BradenMeyers/Unzipper/NON CODE/CAD files/STL/48T Pulley v1.stl

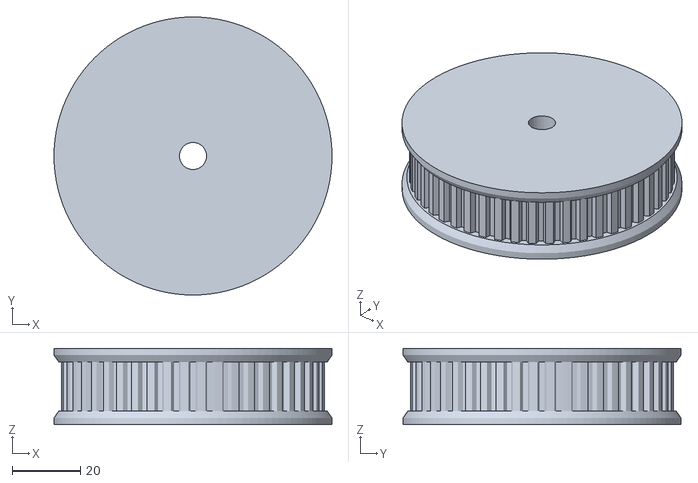
[picture p19: CAD file, 2022-12-04]
NON CODE/CAD files/STL/48T Pulley v1.stl
81.4 x 81.4 x 22.3
