BradenMeyers/Unzipper/src/serverESP.cpp

#include <Arduino.h>
#include <WiFi.h>
#include <AsyncTCP.h>
#include <ESPAsyncWebServer.h>
#include <serverESP.h>
#include <SPIFFS.h>
#include <accelerometer.h>
#include <testCases.h>
#include <odometer.h>
#include <gps.h>
#include <servoBrake.h>

Blogger logger;

typedef enum{
    ACCELEROMETER,
    ODOMETER, 
    LED,
    MOTOR,
    SERVO
} server_test;
server_test testServer = LED;

//#include <constants.h>
#include <Preferences.h>
Preferences preferences;
#include <timer.h>
Timer batterycheck;

const char* ssid = "Zip-Line-Controls";
const char* password = "123456789";

byte batteryMonitor = 34;
byte odometerSensor = 33;

byte state = READY;
int odometerSensorValue = 0;
int motorsMaxSpeed = 200;
float afterZipDelay = 7;

int highThreshold = 3000;
String highThresholdStr = String(highThreshold);
int lowThreshold = 300;
String lowThresholdStr = String(lowThreshold);

String stateStr = "Ready";
String directionStr = "UP";
String motorMaxSpeedStr = String(motorsMaxSpeed);
String afterZipDelayStr = String(afterZipDelay);  //cause actual variable is in miliseconds but wifi is in seconds
String uprightErrorStr = String(uprightError);
String gpsErrorStr = String(gpsError);
String stopPosServoStr = String(stopPosServo);

bool wifiStopMotor = false;
bool wifiSkipToRecovery = false;

AsyncWebServer server(80);

float batteryVoltage(){
    float reading = analogRead(batteryMonitor);
    reading = ((reading)/(4095)) * 25.6;  //calibrated on May 24 2023
    static float voltage = 19.68;
    float alpha = 0.8;
    voltage = voltage*alpha + (1-alpha)*reading;
    return voltage;
}

// Replaces placeholder with button section in your web page
String processor(const String& var){
  //logln(var);
  if (var == "MAXSPEEDVALUE"){return String(motorsMaxSpeed);}
  else if(var == "STATE"){return stateStr;}
  else if(var == "DIRECTION"){return directionStr;}
  else if(var == "AFTERZIPDELAY"){return afterZipDelayStr;}
  else if(var == "LOWTHRESHOLD"){return lowThresholdStr;}
  else if(var == "HIGHTHRESHOLD"){return highThresholdStr;}
  else if(var == "UPRIGHTERROR"){return String(uprightError);}
  else if(var == "VOLTAGE") return String(batteryVoltage());
  else if(var == "TEMPERATURE") return String(getTemperature());
  else if(var == "LOGSTRING"){return logger.logStr.c_str();}
  else if(var == "TESTLOG"){return testLogger.logStr.c_str();}
  else if(var == "SATLOCK"){return String(satelliteLock());}
  else if(var == "GPSERROR"){return String(gpsError);}
  else if(var == "SERVOANGLE"){return String(stopPosServo);}
  return String();
}

void storeValues(){
    preferences.putUInt("lower", lowThreshold);
    preferences.putUInt("upper", highThreshold);
    preferences.putUInt("max", motorsMaxSpeed);
    preferences.putFloat("zDelay", afterZipDelay);
    preferences.putFloat("uError", uprightError);
    preferences.putFloat("gpsError", gpsError);
    preferences.putUInt("servoAngle", stopPosServo);
}

void initSPIFFS() {
  if (!SPIFFS.begin()) {
    Serial.println("An error has occurred while mounting SPIFFS");
  }
  Serial.println("SPIFFS mounted successfully");
}

void serverSetup(){
    preferences.begin("my-app", false);
    motorsMaxSpeed = preferences.getUInt("max", 195);     //max speed
    highThreshold = preferences.getUInt("upper", 2500); //Upper IR Threshold
    lowThreshold = preferences.getUInt("lower", 1000); //Lower IR threshold
    afterZipDelay = preferences.getFloat("zDelay", 10);  //Delay after the zipping state
    uprightError = preferences.getFloat("uError", 1.5);  //Delay after the zipping state
    gpsError = preferences.getFloat("gpsError", 3);  //Delay after the zipping state
    stopPosServo = preferences.getUInt("servoAngle", 133);  //Delay after the zipping state
    motorMaxSpeedStr = String(motorsMaxSpeed);
    afterZipDelayStr = String(afterZipDelay);
    lowThresholdStr = String(lowThreshold);
    highThresholdStr = String(highThreshold);
    uprightErrorStr = String(uprightError);
    gpsErrorStr = String(gpsError);
    stopPosServoStr = String(stopPosServo);
    WiFi.mode(WIFI_AP_STA);
    WiFi.softAP(ssid, password);
    server.begin();
    initSPIFFS();
    delay(3000);

    server.on("/", HTTP_GET, [](AsyncWebServerRequest *request){
        request->send(SPIFFS, "/index.html", String(), false, processor);
    });

    server.on("/maxspeed", HTTP_GET, [] (AsyncWebServerRequest *request){
        // GET input1 value on <ESP_IP>/slider?value=<inputMessage>
        if (request->hasParam("value")) {
        motorMaxSpeedStr = request->getParam("value")->value();
        motorsMaxSpeed = motorMaxSpeedStr.toInt();
        logger.log("Max speed in now: ", true);
        logger.log(motorMaxSpeedStr);
        }
        request->send(200, "text/plain", "OK");
    });

    server.on("/afterzipdelay", HTTP_GET, [] (AsyncWebServerRequest *request){
        // GET input1 value on <ESP_IP>/slider?value=<inputMessage>
        if (request->hasParam("value")) {
        afterZipDelayStr = request->getParam("value")->value();
        afterZipDelay = afterZipDelayStr.toFloat();
        logger.log("After zip delay is now: ", true);
        logger.log(afterZipDelayStr);
        }
        request->send(200, "text/plain", "OK");
    });
    server.on("/uprightError", HTTP_GET, [] (AsyncWebServerRequest *request){
        // GET input1 value on <ESP_IP>/slider?value=<inputMessage>
        if (request->hasParam("value")) {
        uprightErrorStr = request->getParam("value")->value();
        uprightError = uprightErrorStr.toFloat();
        logger.log("Upright Error is now: ", true);
        logger.log(uprightErrorStr);
        }
        request->send(200, "text/plain", "OK");
    });
    server.on("/gpsError", HTTP_GET, [] (AsyncWebServerRequest *request){
        // GET input1 value on <ESP_IP>/slider?value=<inputMessage>
        if (request->hasParam("value")) {
        gpsErrorStr = request->getParam("value")->value();
        gpsError = gpsErrorStr.toFloat();
        logger.log("GPS Error is now: ", true);
        logger.log(gpsErrorStr);
        }
        request->send(200, "text/plain", "OK");
    });
    server.on("/servoangle", HTTP_GET, [] (AsyncWebServerRequest *request){
        // GET input1 value on <ESP_IP>/slider?value=<inputMessage>
        if (request->hasParam("value")) {
        stopPosServoStr = request->getParam("value")->value();
        stopPosServo = stopPosServoStr.toInt();
        logger.log("Servo angle is now: ", true);
        logger.log(stopPosServoStr);
        }
        request->send(200, "text/plain", "OK");
    });

    server.on("/stopclick", HTTP_GET, [](AsyncWebServerRequest *request){
        if(state == RECOVERY){wifiStopMotor = true;}
        Serial.println("stop Button clicked");
        request->send(SPIFFS, "/index.html", String(), false, processor);
    });

    server.on("/directionclick", HTTP_GET, [](AsyncWebServerRequest *request){
        if (directionStr == "UP")
          directionStr = "DOWN";
        else   
          directionStr = "UP";
        request->send(SPIFFS, "/index.html", String(), false, processor);
    });

    server.on("/goupclick", HTTP_GET, [](AsyncWebServerRequest *request){
        if(state == READY){wifiSkipToRecovery = true;}
        Serial.println("go Button clicked");
        request->send(SPIFFS, "/index.html", String(), false, processor);
    });

    server.on("/odometersettingsclick", HTTP_GET, [](AsyncWebServerRequest *request){
        request->send(SPIFFS, "/odometer.html", String(), false, processor);
    });

    server.on("/back", HTTP_GET, [](AsyncWebServerRequest *request){
        if(state == TEST){
            state = READY;
        }
        request->send(SPIFFS, "/index.html", String(), false, processor);
    });

    server.on("/logclick", HTTP_GET, [](AsyncWebServerRequest *request){
        request->send(SPIFFS, "/logger.html", String(), false, processor);
    });

    server.on("/clearlog", HTTP_GET, [](AsyncWebServerRequest *request){
        logger.clearLog();
        Serial.println("CLEARING LOG----");
        request->send(SPIFFS, "/logger.html", String(), false, processor);
    });

    server.on("/disableMainHE", HTTP_GET, [](AsyncWebServerRequest *request){
        disableOdometer(odometerHallEffect);
        logger.log("Disabled main HE sensor", true);
        request->send(SPIFFS, "/odometer.html", String(), false, processor);
    });
    server.on("/disablebackupHE", HTTP_GET, [](AsyncWebServerRequest *request){
        disableOdometer(odometerHallBackup);
        logger.log("Disabled backup HE sensor", true);
        request->send(SPIFFS, "/odometer.html", String(), false, processor);
    });
    server.on("/resetStable", HTTP_GET, [](AsyncWebServerRequest *request){
        setStable();
        logger.log("Stable reset", true);
        request->send(SPIFFS, "/odometer.html", String(), false, processor);
    });
    server.on("/resetGPS", HTTP_GET, [](AsyncWebServerRequest *request){
        resetGPShome();
        request->send(SPIFFS, "/odometer.html", String(), false, processor);
    });
    server.on("/testclick", HTTP_GET, [](AsyncWebServerRequest *request){
        state = TEST;
        request->send(SPIFFS, "/test.html", String(), false, processor);
    });
    server.on("/motortest", HTTP_GET, [](AsyncWebServerRequest *request){
        web_select(MOTOR);
        request->send(SPIFFS, "/test.html", String(), false, processor);
    });
    server.on("/acceltest", HTTP_GET, [](AsyncWebServerRequest *request){
        web_select(ACCELEROMETER);
        request->send(SPIFFS, "/test.html", String(), false, processor);
    });
    server.on("/odomtest", HTTP_GET, [](AsyncWebServerRequest *request){
        web_select(ODOMETER);
        request->send(SPIFFS, "/test.html", String(), false, processor);
    });
    server.on("/servotest", HTTP_GET, [](AsyncWebServerRequest *request){
        web_select(SERVO);
        request->send(SPIFFS, "/test.html", String(), false, processor);
    });
    pinMode(batteryMonitor, INPUT);
    batterycheck.start();
}

void serverLoop(){
    if(batterycheck.getTime() > 5000){
        float volts = batteryVoltage();
        batterycheck.start();
        storeValues();
    }
    logger.checkLogLength();
}
