BradenMeyers/Unzipper/include/serverESP.h

#ifndef SERVERESP
#define SERVERESP

#include <Arduino.h>
#include <string>
// #include <iostream>

#include <Preferences.h>
extern Preferences preferences;

#define READY 1
#define ZIPPING 2
#define RECOVERY 3
#define TEST 4

extern byte state;
extern String stateStr;

extern byte odometerSensor;
extern int odometerSensorValue;

extern int motorsMaxSpeed;
extern String motorMaxSpeedStr;
extern float afterZipDelay;
extern String afterZipDelayStr;  //cause actual variable is in miliseconds but wifi is in seconds
extern String directionStr;
extern bool wifiStopMotor;
extern bool wifiSkipToRecovery;

extern int highThreshold;
extern String highThresholdStr;
extern int lowThreshold;
extern String lowThresholdStr;

void serverSetup();

void serverLoop();


class Logger{
public:
  String(logStr) = "";
  String newLine = "<br>";
  void log(const char* message, bool ln=false){
    if(ln){
      logNewLine();
    }
    logStr = message + logStr;
    Serial.print(message);
  }
  void log(String string, bool ln=false){
    if(ln){
      logNewLine();
    }
    logStr = string + logStr;
    Serial.print(string);
  }
  void log(int i, bool ln=false){
    if(ln){
      logNewLine();
    }
    logStr = String(i) + logStr;
    Serial.print(i);
  }
  void log(unsigned long l, bool ln=false){
    Serial.print(l);
    if(ln){
      logNewLine();
    }
    logStr = String(l) + logStr;
  }
  void logNewLine(){
    Serial.println();
    logStr = newLine + logStr;
    logStr = millis() * 0.001 + logStr;
    logStr = " - " + logStr;
  }
  void checkLogLength(){
    if(logStr.length() > 1100){
      logStr = logStr.substring(100);
    }
  }
  void clearLog(){
    logStr = "";
  }
};

class Blogger{
public:
  std::string logStr = "";
  std::string newLine = "<br>";
  int i = 0;
  void log(const char* message, bool ln=false){
    checkLogLength();   //the esp was reseting possibly because the message was getting too long. 
    Serial.print(message);
    if(ln)
      logNewLine();
    else
      Serial.println();
    i = logStr.find('-', 0);
    if( i != std::string::npos) {
      logStr.insert((i - 1), message);
    } else {
      logStr += message;
    }
  }
  void log(String string, bool ln=false){
    const char* message = string.c_str();
    checkLogLength();
    Serial.print(message);
    if(ln)
      logNewLine();
    else
      Serial.println();
    i = logStr.find('-', 0);
    if( i != std::string::npos){
      logStr.insert((i - 1), message);
    } else {
      logStr += message;
    }
  }
  void log(int integer, bool ln=false){
    std::string message = std::to_string(integer);
    checkLogLength();
    Serial.print(integer);
    if(ln)
      logNewLine();
    else
      Serial.println();
    i = logStr.find('-', 0);
    if( i != std::string::npos){
      logStr.insert((i - 1), message);
    } else {
      logStr += message;
    }
  }
  void log(double integer, bool ln=false){
    std::string message = std::to_string(integer);
    checkLogLength();
    Serial.print(integer);
    if(ln)
      logNewLine();
    else
      Serial.println();
    i = logStr.find('-', 0);
    if( i != std::string::npos){
      logStr.insert((i - 1), message);
    } else {
      logStr += message;
    }
  }
  void log(unsigned long l, bool ln=false){
    std::string message = std::to_string(l);
    checkLogLength();
    Serial.print(l);
    if(ln)
      logNewLine();
    else
      Serial.println();
    i = logStr.find('-', 0);
    if( i != std::string::npos){
      logStr.insert((i - 1), message);
    } else {
      logStr += message;
    }
  }
  void logNewLine(){
    logStr = newLine + logStr;
    logStr = std::to_string(int(millis() * 0.001)) + logStr;
    logStr = " - " + logStr;
  }
  void checkLogLength(){
    if(logStr.length() > 1000){
      logStr.resize(100);
      Serial.println("shortened log");
    }
  }
  void clearLog(){
    logStr = "";
  }
};

extern Blogger logger;

float batteryVoltage();

#endif
